supernach00/Broadband-Microwave-Noise-Generator/SPICE/Doble.asc

Amp1: res; 0.0001
Amp2: res; 0.0001
C1: cap; 10n
C2: cap; 22n
C3: cap; 100n
C4: cap; 22n
Q1: pnp; BD140
Q2: pnp; BD140
R1: res; 5600
R2: res; 22
R3: res; 5600
R4: res; 22
R5: res; 0
R8: res; 0
R11: res; 51
RF_CHOKE_1: ind; 15µ
RF_CHOKE_2: ind; 15µ
sma_connector: res; 50
U1: TL431
U2: TL431
Vcc: voltage; 35
Zener1: zener; BZX84B22VL
Zener2: zener; BZX84B22VL
Named nets: Vcc, 0, Vout
.tran .10
