supernach00/Broadband-Microwave-Noise-Generator/SPICE/Simple.asc

Amperímetro: res; 0.000001
C1: cap; 10n
C2: cap; 22n
C3: cap; 100n
L1: ind; 15µ
Q1: pnp; BD140
R1: res; 5600
R2: res; 22
R3: res; 51
R4: res; 5k
R5: res; 5k
R6: res; 50
U1: TL431
U2: TL431
Vcc1: voltage; 3
Vcc: voltage; 30
Zener: zener; BZX84B22VL
Named nets: 0, Vout
.tran .10
Corriente máxima: (Vcc - Veb_max)/(R2 + Pmin) = (2.5 - 0.7)/(22) = 81.8mA
Corriente mínima: (Vcc - Veb_min)/(R2 + Pmax) = (2.5 - 0.54)/(5k + 22) = 0.39mA
Test de polarización TL431
Test 1 etapa
